balerion/ppg-instrument/Arduino code/src/graphics.h

#define mouth1_width 128
#define mouth1_height 32
static const unsigned char mouth1_bits[] = {
  0x00, 0xF0, 0xFF, 0xFF, 0xFF, 0xFF, 0xFF, 0xFF, 0xFF, 0xFF, 0xFF, 0xFF, 
  0xFF, 0xFF, 0x07, 0x00, 0x00, 0xFF, 0xFF, 0xFF, 0xFF, 0xFF, 0xFF, 0xFF, 
  0xFF, 0xFF, 0xFF, 0xFF, 0xFF, 0xFF, 0x7F, 0x00, 0x80, 0xFF, 0x3F, 0x00, 
  0xC0, 0x0F, 0x00, 0xF0, 0x03, 0x00, 0xF8, 0x03, 0x00, 0xFC, 0xFF, 0x00, 
  0xF0, 0x0F, 0x0E, 0x00, 0x00, 0x07, 0x00, 0xC0, 0x01, 0x00, 0xE0, 0x00, 
  0x00, 0x38, 0xFC, 0x07, 0xFC, 0x0F, 0x0E, 0x00, 0x00, 0x07, 0x00, 0xC0, 
  0x01, 0x00, 0xE0, 0x00, 0x00, 0x38, 0xF0, 0x1F, 0xFC, 0x01, 0x0E, 0x00, 
  0x00, 0x07, 0x00, 0xC0, 0x01, 0x00, 0xE0, 0x00, 0x00, 0x38, 0xC0, 0x3F, 
  0x7F, 0x00, 0x0E, 0x00, 0x00, 0x07, 0x00, 0xC0, 0x01, 0x00, 0xE0, 0x00, 
  0x00, 0x38, 0x00, 0x7F, 0x7F, 0x00, 0x0E, 0x00, 0x00, 0x07, 0x00, 0xC0, 
  0x01, 0x00, 0xE0, 0x00, 0x00, 0x38, 0x00, 0xFE, 0x3F, 0x00, 0x0E, 0x00, 
  0x00, 0x07, 0x00, 0xC0, 0x01, 0x00, 0xE0, 0x00, 0x00, 0x38, 0x00, 0xFE, 
  0x3F, 0x00, 0x0E, 0x00, 0x00, 0x07, 0x00, 0xE0, 0xFF, 0x00, 0xE0, 0x00, 
  0x00, 0x38, 0x00, 0xFC, 0x3F, 0x00, 0x0E, 0x00, 0x00, 0x07, 0xF0, 0xFF, 
  0xFF, 0x3F, 0xE0, 0x00, 0x00, 0x3C, 0x00, 0xFC, 0x3F, 0x00, 0x0E, 0x00, 
  0x00, 0x07, 0xFE, 0xFF, 0x01, 0xFF, 0xE3, 0x00, 0x00, 0x1C, 0x00, 0xFC, 
  0x3F, 0x00, 0x0E, 0x00, 0x00, 0xFF, 0x7F, 0xC0, 0x01, 0xC0, 0xFF, 0x01, 
  0x00, 0x1C, 0x00, 0xFC, 0xFF, 0xFF, 0xFF, 0xFF, 0xFF, 0xFF, 0x01, 0xC0, 
  0x01, 0x00, 0xFF, 0xFF, 0xFF, 0xFF, 0xFF, 0xFF, 0xFF, 0xFF, 0xFF, 0xFF, 
  0xFF, 0x07, 0x00, 0xC0, 0x01, 0x00, 0xE0, 0xFF, 0xFF, 0xFF, 0xFF, 0xFF, 
  0x3F, 0x00, 0x1E, 0x00, 0x00, 0x07, 0x00, 0xC0, 0x01, 0x00, 0xE0, 0x00, 
  0x00, 0x1C, 0x00, 0xFC, 0x3F, 0x00, 0x1C, 0x00, 0x00, 0x07, 0x00, 0xC0, 
  0x01, 0x00, 0xE0, 0x00, 0x00, 0x1C, 0x00, 0xFC, 0x3F, 0x00, 0x1C, 0x00, 
  0x00, 0x07, 0x00, 0xC0, 0x01, 0x00, 0xE0, 0x00, 0x00, 0x1C, 0x00, 0xFC, 
  0xFF, 0x0F, 0x1C, 0x00, 0x00, 0x07, 0x00, 0xC0, 0x01, 0x00, 0xE0, 0x00, 
  0x00, 0x1C, 0x00, 0xFC, 0xFF, 0xFF, 0x3F, 0x00, 0x00, 0x07, 0x00, 0xC0, 
  0x01, 0x00, 0xE0, 0x00, 0x00, 0x1C, 0x00, 0xFC, 0x3F, 0xFC, 0xFF, 0x7F, 
  0x00, 0x07, 0x00, 0xC0, 0x01, 0x00, 0xE0, 0x00, 0x00, 0xFC, 0xFF, 0xFF, 
  0x3F, 0x00, 0xFC, 0xFF, 0x3F, 0x07, 0x00, 0xC0, 0x01, 0x00, 0xE0, 0xC0, 
  0xFF, 0xFF, 0xFF, 0xFF, 0x3F, 0x00, 0x38, 0xFE, 0xFF, 0xFF, 0x01, 0xC0, 
  0x01, 0xFC, 0xFF, 0xFF, 0xFF, 0x1F, 0x00, 0xFC, 0x7F, 0x00, 0x38, 0x00, 
  0xF8, 0xFF, 0xFF, 0xFF, 0xFF, 0xFF, 0xFF, 0x3F, 0x00, 0x1C, 0x00, 0x7E, 
  0x7E, 0x00, 0x38, 0x00, 0x00, 0x0F, 0xFF, 0xFF, 0xFF, 0x07, 0x70, 0x00, 
  0x00, 0x1C, 0x00, 0x7F, 0xFE, 0x00, 0x38, 0x00, 0x00, 0x07, 0x00, 0xC0, 
  0x01, 0x00, 0x70, 0x00, 0x00, 0x1C, 0x00, 0x7F, 0xFC, 0x01, 0x38, 0x00, 
  0x00, 0x07, 0x00, 0xC0, 0x01, 0x00, 0x70, 0x00, 0x00, 0x1C, 0xC0, 0x3F, 
  0xF8, 0x07, 0x38, 0x00, 0x00, 0x07, 0x00, 0xC0, 0x01, 0x00, 0x70, 0x00, 
  0x00, 0x1C, 0xE0, 0x1F, 0xF0, 0x1F, 0x38, 0x00, 0x00, 0x07, 0x00, 0xC0, 
  0x01, 0x00, 0x70, 0x00, 0x00, 0x1C, 0xFC, 0x07, 0xC0, 0x7F, 0x38, 0x00, 
  0x00, 0x07, 0x00, 0xC0, 0x01, 0x00, 0x70, 0x00, 0x00, 0x1C, 0xFC, 0x01, 
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
